ArrestedLightning/kilosegment_clock/Firmware/kilosegment_clock_firmware/src/kilosegment_clock_firmware.h

#pragma once
#include <Arduino.h>

void handleCLIUSB(void);
void handleCLISerial(void);
void updateRTCandSettings(void);
void testButtons(void);
void clockButtonPressed(void);
void clockButtonHeld(void);
void enterButtonPressed(void);
void downButtonPressed(void);
void upButtonPressed(void);
bool cancelAlarm(void);
void switchToDateScreen(void);
void showSetup(bool force);
uint8_t hour_24_to_12(uint8_t hour, bool format_12hr);
void showTime(bool force);
void showTime(int h, int m, bool he, bool me, bool ce, bool f24);
void showDate(int d, int m, int y);
void displayDateDigit(uint8_t x, uint8_t v);
void displayLargeDigit(uint8_t x, uint8_t v);
void displaySmallDigit(uint8_t x, uint8_t v);
void displaySquareDigit(uint8_t col, uint8_t v);
void displayString(uint8_t row, uint8_t col, String s);
void displayNumber(uint8_t row, uint8_t col, int number, int padding, bool leadingZeros);
void writePhysicalDigit(uint8_t row, uint8_t col, uint8_t v, bool erase);
uint8_t daysInMonth(int y, int m);
void writeEepromData(void);
bool readEepromData(void);
void makeSettingsString(char *str, size_t length);
void playSong(const uint16_t* melody);
void playNote(uint16_t noteRaw);
void clearDisplay(void);
void updateDisplay(void);
void setDisplayBrightness(uint8_t dispBrightness);
uint16_t tmYearToCalendar(uint8_t year);
uint8_t tmYearFromCalendar(uint16_t cYear);
uint32_t getSecondOfDay(void);
void readLightSensor(void);
void loadDefaults(void);
void feed_watchdog(void);
