ArrestedLightning/kilosegment_clock/Firmware/kilosegment_clock_firmware/src/mapping.h

#pragma once

#include <stdint.h>

//maps logical digit to the physical display driver
//arranged as y, x
static const uint8_t device_mapping[6][24] = {
{ 0,  0,  0,  0,  0,  0,  0,  0,  0,  0,  0,  0,  0,  0,  0,  0,  6,  6,  6,  6,  6,  6,  6,  6 },
{ 1,  1,  1,  1,  1,  1,  1,  1,  1,  1,  1,  1,  1,  1,  1,  1,  6,  6,  6,  6,  6,  6,  6,  6 },
{ 2,  2,  2,  2,  2,  2,  2,  2,  2,  2,  2,  2,  2,  2,  2,  2,  7,  7,  7,  7,  7,  7,  7,  7 },
{ 3,  3,  3,  3,  3,  3,  3,  3,  3,  3,  3,  3,  3,  3,  3,  3,  7,  7,  7,  7,  7,  7,  7,  7 },
{ 4,  4,  4,  4,  4,  4,  4,  4,  4,  4,  4,  4,  4,  4,  4,  4,  8,  8,  8,  8,  8,  8,  8,  8 },
{ 5,  5,  5,  5,  5,  5,  5,  5,  5,  5,  5,  5,  5,  5,  5,  5,  8,  8,  8,  8,  8,  8,  8,  8 },
};

//maps logical digit to the per-device physical digit
//arranged as y, x
static const uint8_t digit_mapping[6][24] = {
{ 0,  1,  2,  3,  4,  5,  6,  7,  8,  9,  10,  11,  12,  13,  14,  15,  0,  1,  2,    3,   4,   5,   6,  7  },
{ 0,  1,  2,  3,  4,  5,  6,  7,  8,  9,  10,  11,  12,  13,  14,  15,  8,  9,  10,  11,  12,  13,  14,  15 },
{ 0,  1,  2,  3,  4,  5,  6,  7,  8,  9,  10,  11,  12,  13,  14,  15,  0,  1,  2,    3,   4,   5,   6,  7  },
{ 0,  1,  2,  3,  4,  5,  6,  7,  8,  9,  10,  11,  12,  13,  14,  15,  8,  9,  10,  11,  12,  13,  14,  15 },
{ 0,  1,  2,  3,  4,  5,  6,  7,  8,  9,  10,  11,  12,  13,  14,  15,  0,  1,  2,    3,   4,   5,   6,  7  },
{ 0,  1,  2,  3,  4,  5,  6,  7,  8,  9,  10,  11,  12,  13,  14,  15,  8,  9,  10,  11,  12,  13,  14,  15 },
};
