ArrestedLightning/kilosegment_clock/Firmware/kilosegment_clock_firmware/src/kilosegment_clock_bootloader.h

#pragma once
#include <stdint.h>
/* Bootloader is from https://github.com/ArrestedLightning/STM32_HID_Bootloader
 * compiled with `make kilosegment-clock` */
#ifdef EMBED_BOOTLOADER
const uint8_t bootloader_only_binaries_kilosegment_clock_bin[] __attribute__((section(".bl_flash"), __used__)) = {
  0x00, 0x50, 0x00, 0x20, 0x15, 0x00, 0x00, 0x08, 0x00, 0x23, 0x00, 0xbf,
  0x01, 0x33, 0x98, 0x42, 0xfb, 0xd1, 0x70, 0x47, 0xf8, 0xb5, 0x4d, 0x4c,
  0x00, 0xaf, 0x23, 0x68, 0x43, 0xf4, 0x80, 0x33, 0x23, 0x60, 0x23, 0x68,
  0x9d, 0x03, 0xfc, 0xd5, 0x49, 0x4a, 0x13, 0x68, 0x43, 0xf0, 0x12, 0x03,
  0x13, 0x60, 0x63, 0x68, 0x43, 0xf4, 0xe8, 0x13, 0x43, 0xf4, 0x80, 0x63,
  0x63, 0x60, 0x23, 0x68, 0x43, 0xf0, 0x80, 0x73, 0x23, 0x60, 0x23, 0x68,
  0x98, 0x01, 0xfc, 0xd5, 0x63, 0x68, 0x43, 0xf0, 0x02, 0x03, 0x63, 0x60,
  0x63, 0x68, 0x19, 0x07, 0xfc, 0xd5, 0x4f, 0xf0, 0x00, 0x53, 0x3d, 0x4a,
  0x3d, 0x49, 0x1a, 0x60, 0x3d, 0x4a, 0x5a, 0x60, 0x3d, 0x4a, 0xc3, 0xf8,
  0x90, 0x20, 0x3d, 0x4a, 0x93, 0x60, 0xe3, 0x69, 0x43, 0xf0, 0xc0, 0x53,
  0xe3, 0x61, 0x0d, 0x8a, 0xad, 0xb2, 0x55, 0xb1, 0x39, 0x4b, 0x1a, 0x68,
  0x42, 0xf4, 0x80, 0x72, 0x1a, 0x60, 0x00, 0x22, 0x0a, 0x82, 0x1a, 0x68,
  0x22, 0xf4, 0x80, 0x72, 0x1a, 0x60, 0xe3, 0x69, 0x34, 0x4e, 0x23, 0xf0,
  0xc0, 0x53, 0xe3, 0x61, 0x00, 0xf0, 0xe6, 0xfa, 0x48, 0x20, 0xff, 0xf7,
  0xaf, 0xff, 0x00, 0x23, 0x30, 0x4a, 0x33, 0x70, 0x13, 0x70, 0x44, 0xf2,
  0x4c, 0x22, 0x4f, 0xf0, 0x00, 0x63, 0x95, 0x42, 0xd3, 0xf8, 0x04, 0x18,
  0x18, 0xd0, 0x2c, 0x4a, 0x92, 0x68, 0xd2, 0x07, 0x19, 0xd5, 0xd3, 0xf8,
  0x00, 0x08, 0x2a, 0x4a, 0x02, 0x40, 0xb2, 0xf1, 0x00, 0x5f, 0x12, 0xd1,
  0x4f, 0xf0, 0x08, 0x20, 0xa2, 0x69, 0x22, 0xf0, 0x0d, 0x02, 0xa2, 0x61,
  0x1f, 0x4a, 0x90, 0x60, 0xd3, 0xf8, 0x00, 0x38, 0x83, 0xf3, 0x08, 0x88,
  0x88, 0x47, 0xfe, 0xe7, 0x00, 0xf0, 0xd2, 0xf8, 0x20, 0x48, 0xff, 0xf7,
  0x85, 0xff, 0x00, 0xf0, 0xfb, 0xf8, 0x4f, 0xf4, 0x00, 0x41, 0x1e, 0x4a,
  0x1e, 0x4c, 0x19, 0x4b, 0x1b, 0x78, 0x73, 0xb1, 0x00, 0xf0, 0xc4, 0xf8,
  0xbf, 0xf3, 0x4f, 0x8f, 0x12, 0x49, 0x1b, 0x4b, 0xca, 0x68, 0x02, 0xf4,
  0xe0, 0x62, 0x13, 0x43, 0xcb, 0x60, 0xbf, 0xf3, 0x4f, 0x8f, 0x00, 0xbf,
  0xfd, 0xe7, 0x33, 0x78, 0x33, 0xb9, 0x20, 0x46, 0x51, 0x61, 0xff, 0xf7,
  0x67, 0xff, 0x11, 0x61, 0xff, 0xf7, 0x64, 0xff, 0x4f, 0xf4, 0xc8, 0x70,
  0xff, 0xf7, 0x60, 0xff, 0xdf, 0xe7, 0x00, 0xbf, 0x00, 0x10, 0x02, 0x40,
  0x00, 0x20, 0x02, 0x40, 0x00, 0x50, 0x00, 0x20, 0x00, 0x6c, 0x00, 0x40,
  0x15, 0x00, 0x00, 0x08, 0x6d, 0x03, 0x00, 0x08, 0x00, 0xed, 0x00, 0xe0,
  0x00, 0x70, 0x00, 0x40, 0xc8, 0x05, 0x00, 0x20, 0xc9, 0x05, 0x00, 0x20,
  0x00, 0x0c, 0x01, 0x40, 0x00, 0x00, 0xfe, 0x2f, 0x00, 0x09, 0x3d, 0x00,
  0x00, 0x08, 0x01, 0x40, 0x40, 0x0d, 0x03, 0x00, 0x04, 0x00, 0xfa, 0x05,
  0x10, 0xb5, 0x48, 0x24, 0x11, 0x4b, 0x12, 0x49, 0xd3, 0xf8, 0x50, 0x3c,
  0x9b, 0xb2, 0x03, 0xeb, 0xc0, 0x03, 0x03, 0xf1, 0x00, 0x53, 0x04, 0xfb,
  0x00, 0x10, 0x03, 0xf5, 0x40, 0x53, 0x5b, 0x00, 0xda, 0x68, 0x80, 0xf8,
  0x44, 0x20, 0x99, 0x68, 0xd2, 0xb2, 0x01, 0xf1, 0x00, 0x51, 0x01, 0xf5,
  0x40, 0x51, 0x92, 0x00, 0x4b, 0x00, 0x02, 0xeb, 0x41, 0x02, 0x93, 0x42,
  0x00, 0xd1, 0x10, 0xbd, 0x53, 0xf8, 0x04, 0x1b, 0x20, 0xf8, 0x02, 0x1b,
  0xf7, 0xe7, 0x00, 0xbf, 0x00, 0x50, 0x00, 0x40, 0x30, 0x01, 0x00, 0x20,
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
};
//unsigned int bootloader_only_binaries_kilosegment_clock_bin_len = 2048;
#endif
